m-labs/ionpak/pictures/pcb_unassembled.jpg

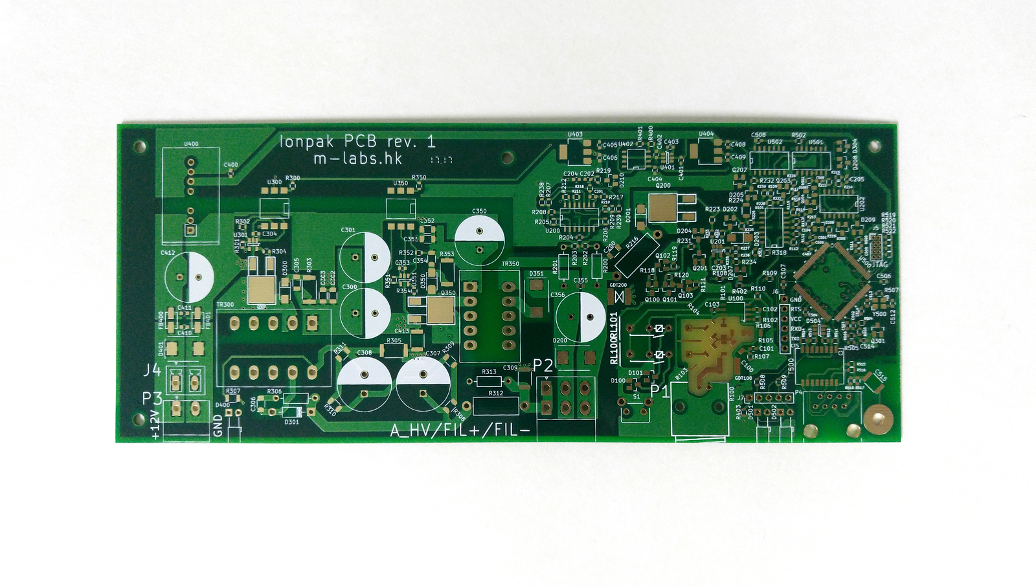
pictures/pcb_unassembled.jpg
